M17-Project/M17_3310/M17_3310.kicad_sch

## KiCad design M17_3310.kicad_sch (2025-02-24)

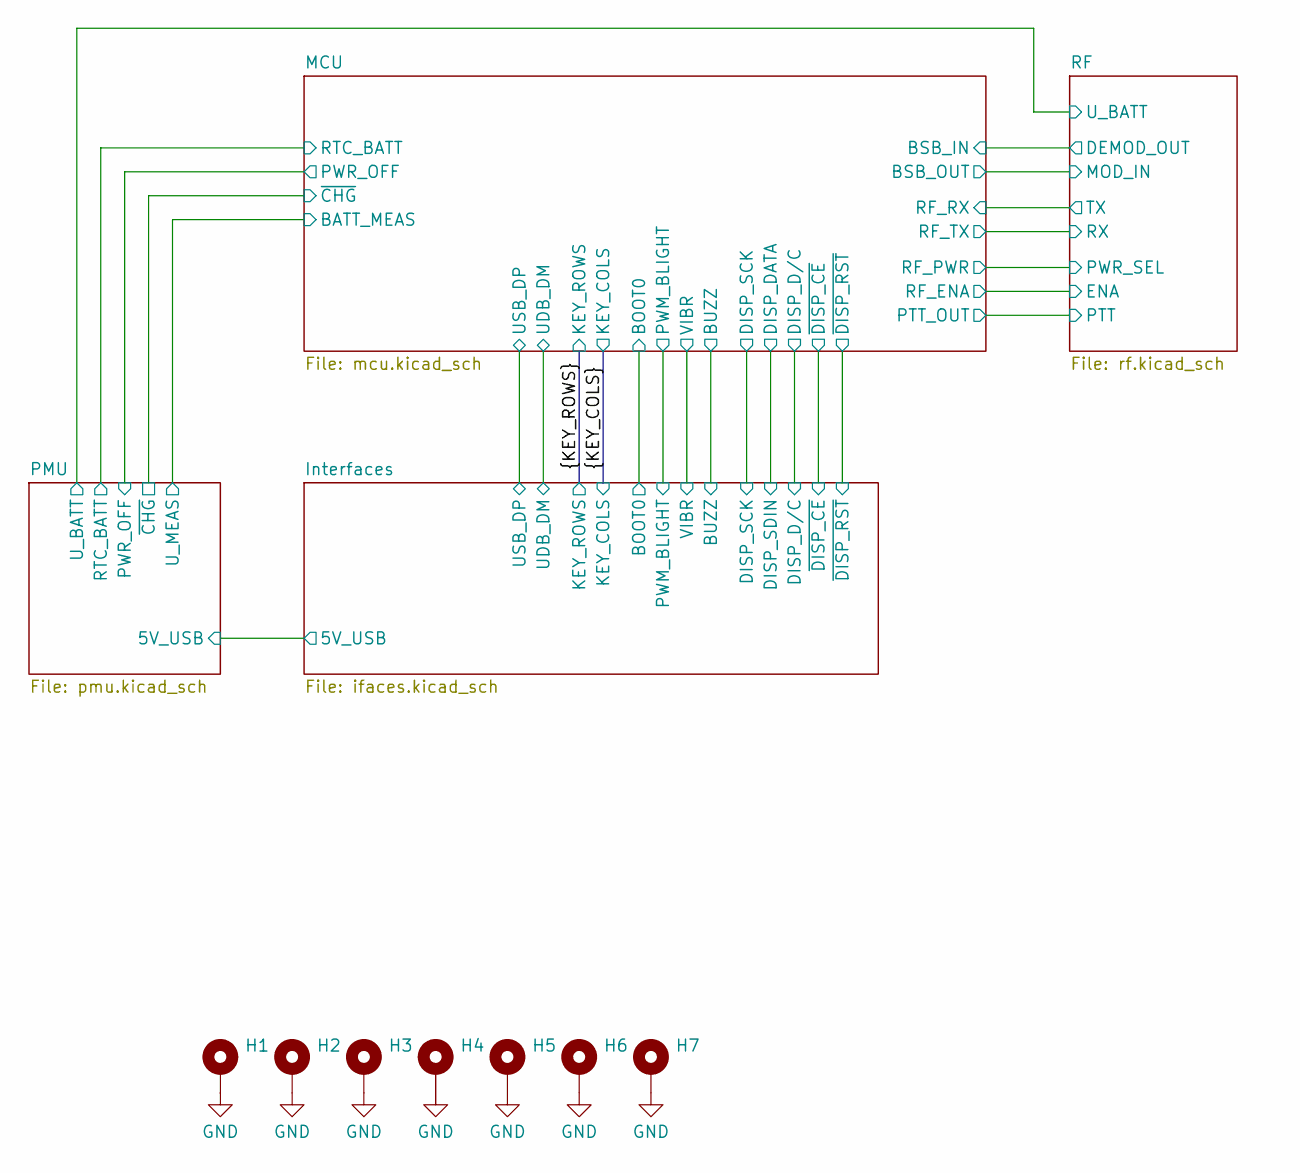
[picture p6: schematic M17_3310.kicad_sch]

Parts:
H1, H2, H3, H4, H5, H6, H7: 2mm_mounting_hole_sig

Connections:
GND: H1.1, H2.1, H3.1, H4.1, H5.1, H6.1, H7.1
