M17-Project/M17_3310/ifaces.kicad_sch

## KiCad design ifaces.kicad_sch (2025-02-24)

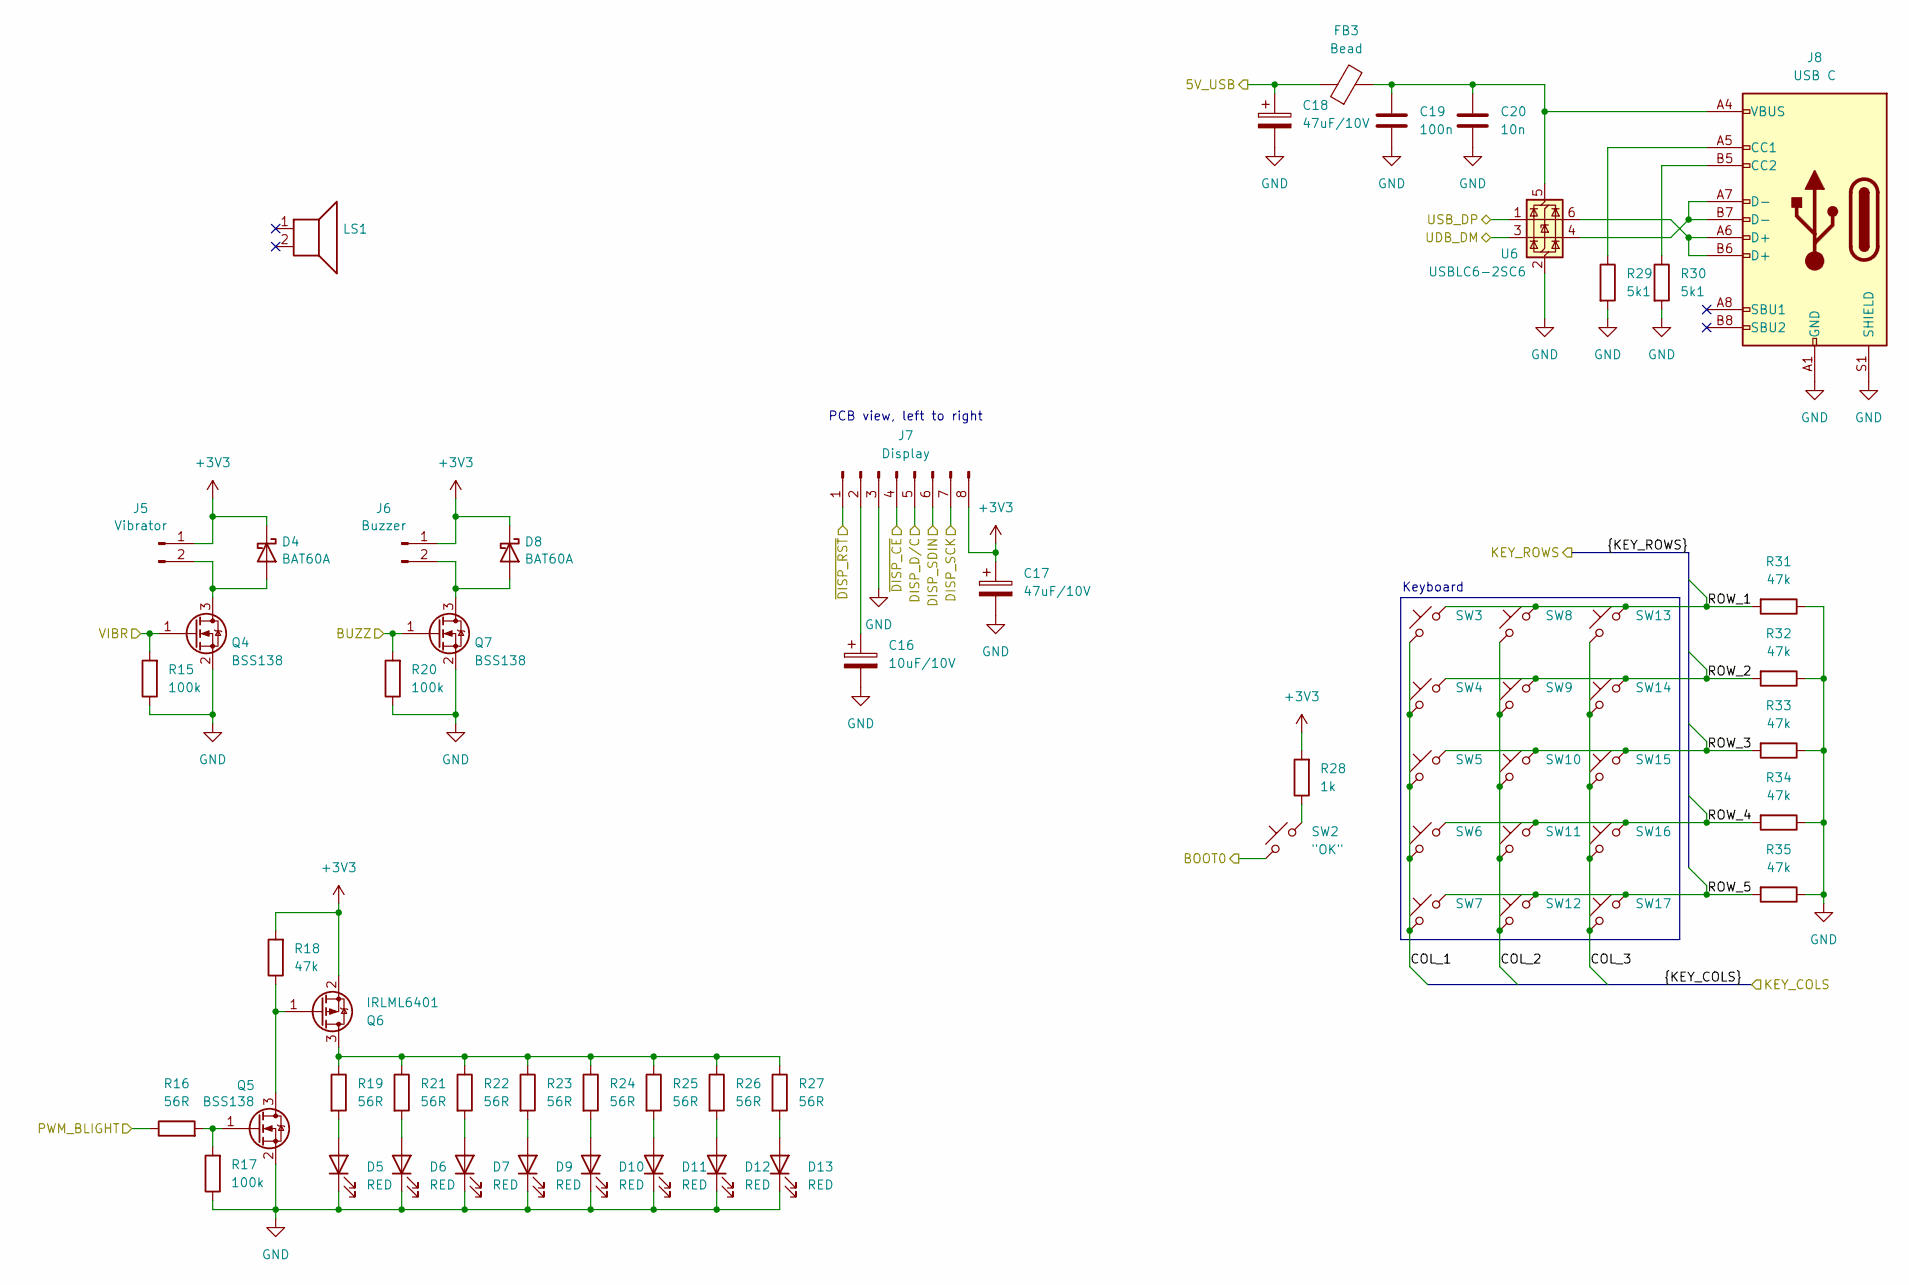
[picture p7: schematic ifaces.kicad_sch]

Parts:
C16: 10uF/10V; CP_EIA-3528-21_Kemet-B; MPN 581-TAJB106K010SNJ
C17, C18: 47uF/10V; CP_EIA-3528-21_Kemet-B; MPN 74-293D476X9010B2TE3
C19: 100n; C_0402_1005Metric; MPN 810-CGA2B3X7R1H104KB
C20: 10n; C_0402_1005Metric; MPN 77-VJ0402Y103KCAAC
D4, D8: BAT60A; D_SOD-323; MPN 726-BAT60AE6327HTSA1
D5, D6, D7, D9, D10, D11, D12, D13: RED; 3310_led; MPN 743-IN-S124ARUR
FB3: Bead; L_0805_2012Metric; MPN 810-MPZ2012S102AT000
J5: Vibrator; 3310_vibrator
J6: Buzzer; 3310_buzzer
J7: Display; 3310_display
J8: USB C; USB_C_Receptacle_GCT_USB4110; MPN 640-USB4110-GF-A
LS1: 3310_speaker
Q4, Q5, Q7: BSS138; SOT-23; MPN 771-BSS138P215
Q6: IRLML6401; SOT-23; MPN 942-IRLML6401TRPBF
R15, R17, R20: 100k; R_0402_1005Metric; MPN 603-RC0402JR-13100KL
R16, R19, R21, R22, R23, R24, R25, R26, R27: 56R; R_0402_1005Metric; MPN 667-ERJ-2GEJ560X
R18, R31, R32, R33, R34, R35: 47k; R_0402_1005Metric; MPN 652-CR0402JW-473GLF
R28: 1k; R_0402_1005Metric; MPN 603-AF0402JR-071KL
R29, R30: 5k1; R_0402_1005Metric; MPN 660-RK73B1ETTP512J
SW2: "OK"; 3310_key
SW3, SW4, SW5, SW6, SW7, SW8, SW9, SW10, SW11, SW12, SW13, SW14, SW15, SW17: 3310_key
SW16: 3310_key_gap
U6: USBLC6-2SC6; SOT-23-6; MPN 511-USBLC6-2SC6

Connections:
5V_USB: C18.1, FB3.1
+3V3: C17.1, D4.1 (K), D8.1 (K), J5.1, J6.1, J7.8, Q6.2 (S), R18.2, R28.2
BOOT0: SW2.1
BUZZ: Q7.1 (G), R20.2
COL_1: SW3.1, SW4.1, SW5.1, SW6.1, SW7.1
COL_2: SW8.1, SW9.1, SW10.1, SW11.1, SW12.1
COL_3: SW13.1, SW14.1, SW15.1, SW16.1, SW17.1
DISP_D/C: J7.5
DISP_SCK: J7.7
DISP_SDIN: J7.6
GND: C16.2, C17.2, C18.2, C19.2, C20.2, D5.1 (K), D6.1 (K), D7.1 (K), D9.1 (K), D10.1 (K), D11.1 (K), D12.1 (K), D13.1 (K), J7.3, J8.A1 (GND), J8.A12 (GND), J8.B1 (GND), J8.B12 (GND), J8.S1 (SHIELD), Q4.2 (S), Q5.2 (S), Q7.2 (S), R15.1, R17.1, R20.1, R29.2, R30.2, R31.1, R32.1, R33.1, R34.1, R35.1, U6.2 (GND)
unnamed: C16.1, J7.2
unnamed: C19.1, C20.1, FB3.2, J8.A4 (VBUS), J8.A9 (VBUS), J8.B4 (VBUS), J8.B9 (VBUS), U6.5 (VBUS)
unnamed: D4.2 (A), J5.2, Q4.3 (D)
unnamed: D5.2 (A), R19.2
unnamed: D6.2 (A), R21.2
unnamed: D7.2 (A), R22.2
unnamed: D8.2 (A), J6.2, Q7.3 (D)
unnamed: D9.2 (A), R23.2
unnamed: D10.2 (A), R24.2
unnamed: D11.2 (A), R25.2
unnamed: D12.2 (A), R26.2
unnamed: D13.2 (A), R27.2
unnamed: J8.A5 (CC1), R29.1
unnamed: J8.A6 (D+), J8.B6 (D+), U6.6 (I/O1)
unnamed: J8.A7 (D-), J8.B7 (D-), U6.4 (I/O2)
unnamed: J8.B5 (CC2), R30.1
unnamed: Q5.1 (G), R16.2, R17.2
unnamed: Q5.3 (D), Q6.1 (G), R18.1
unnamed: Q6.3 (D), R19.1, R21.1, R22.1, R23.1, R24.1, R25.1, R26.1, R27.1
unnamed: R28.1, SW2.2
PWM_BLIGHT: R16.1
ROW_1: R31.2, SW3.2, SW8.2, SW13.2
ROW_2: R32.2, SW4.2, SW9.2, SW14.2
ROW_3: R33.2, SW5.2, SW10.2, SW15.2
ROW_4: R34.2, SW6.2, SW11.2, SW16.2
ROW_5: R35.2, SW7.2, SW12.2, SW17.2
UDB_DM: U6.3 (I/O2)
USB_DP: U6.1 (I/O1)
VIBR: Q4.1 (G), R15.2
~DISP_CE: J7.4
~DISP_RST: J7.1

Notes on the sheet:
Keyboard
PCB view, left to right
