M17-Project/M17_3310/mcu.kicad_sch

## KiCad design mcu.kicad_sch (2025-02-24)

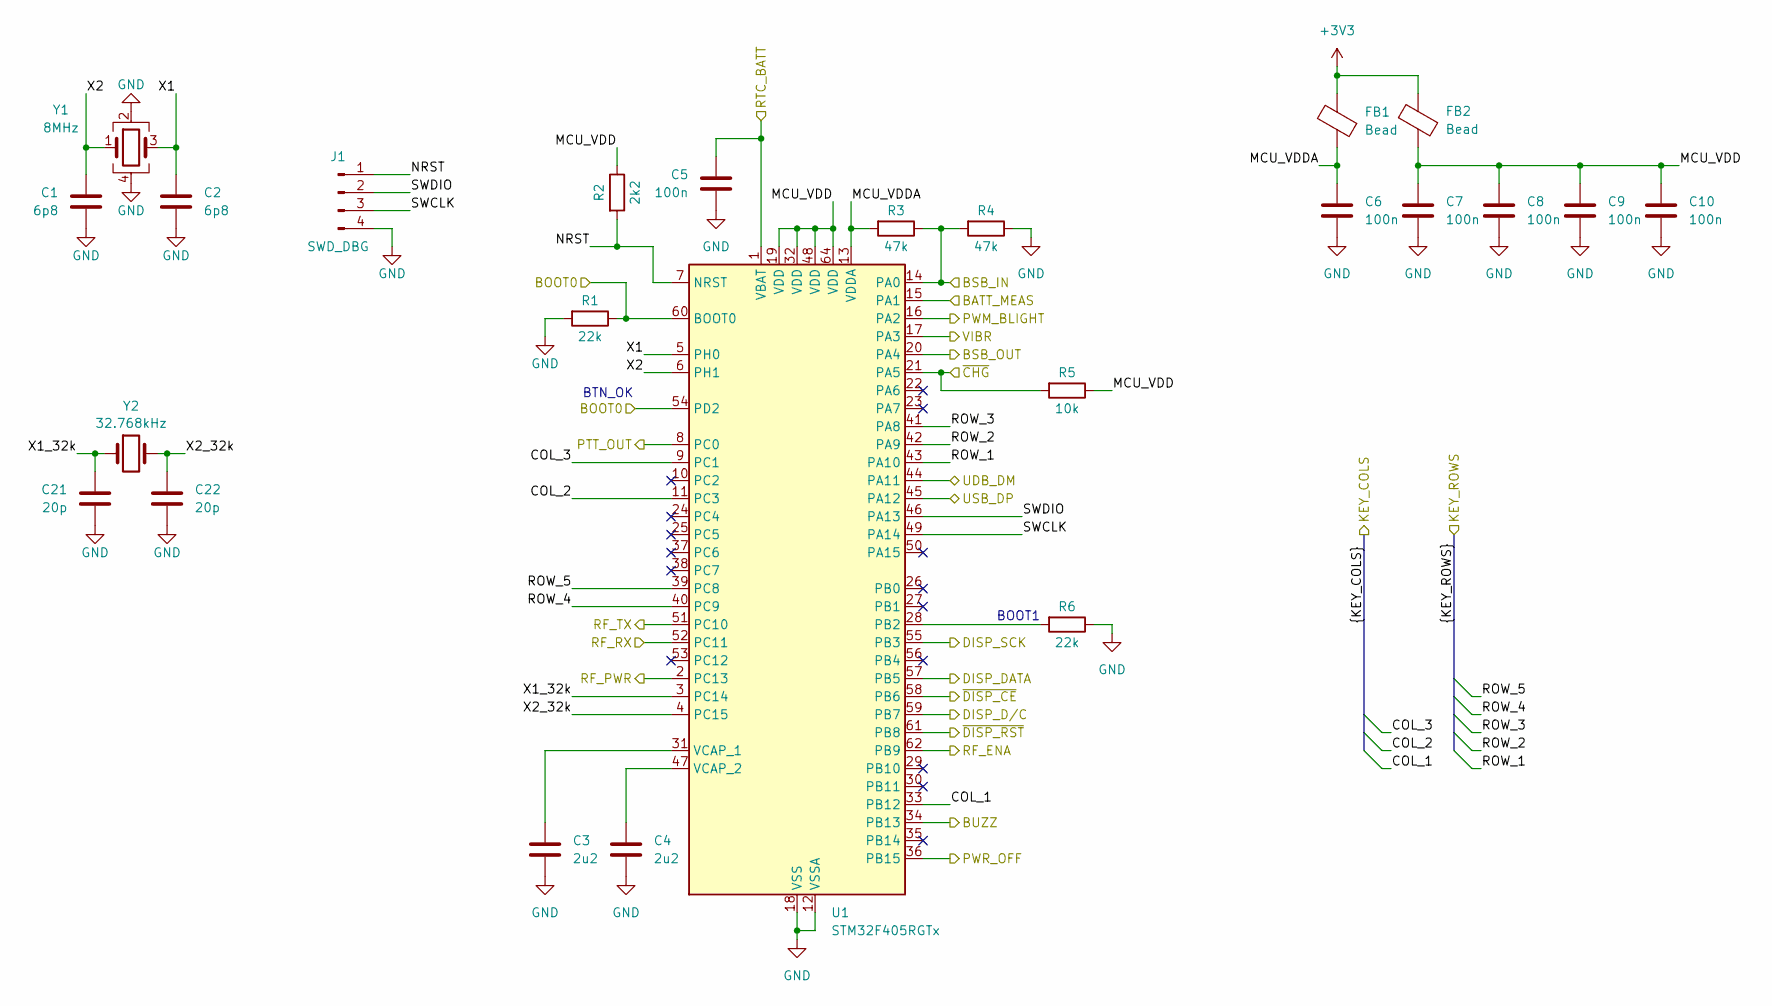
[picture p8: schematic mcu.kicad_sch]

Parts:
C1, C2: 6p8; C_0402_1005Metric; MPN 710-885012005039
C3, C4: 2u2; C_0402_1005Metric; MPN 963-LMK105BJ225MV-F
C5, C6, C7, C8, C9, C10: 100n; C_0402_1005Metric; MPN 810-CGA2B3X7R1H104KB
C21, C22: 20p; C_0402_1005Metric; MPN 81-GCM1555C1H200GA6D
FB1, FB2: Bead; L_0805_2012Metric; MPN 810-MPZ2012S102AT000
J1: SWD_DBG; 3310_4_pin
R1, R6: 22k; R_0402_1005Metric; MPN 279-CRGCQ0402J22K
R2: 2k2; R_0402_1005Metric; MPN 279-CRGCQ0402J2K2
R3, R4: 47k; R_0402_1005Metric; MPN 652-CR0402JW-473GLF
R5: 10k; R_0402_1005Metric; MPN 603-RC0402JR-7D10KL
U1: STM32F405RGTx; LQFP-64_10x10mm_P0.5mm; MPN 511-STM32F405RGT6
Y1: 8MHz; Crystal_SMD_3225-4Pin_3.2x2.5mm; MPN 520-ECS-80-1033CHNTR
Y2: 32.768kHz; xtal_smd_32k

Connections:
+3V3: FB1.2, FB2.1
BATT_MEAS: U1.15 (PA1)
BOOT0: R1.1, U1.54 (PD2), U1.60 (BOOT0)
BSB_IN: R3.1, R4.2, U1.14 (PA0)
BSB_OUT: U1.20 (PA4)
BUZZ: U1.34 (PB13)
COL_1: U1.33 (PB12)
COL_2: U1.11 (PC3)
COL_3: U1.9 (PC1)
DISP_DATA: U1.57 (PB5)
DISP_D/C: U1.59 (PB7)
DISP_SCK: U1.55 (PB3)
GND: C1.2, C2.2, C3.1, C4.1, C5.1, C6.1, C7.2, C8.2, C9.2, C10.2, C21.2, C22.1, J1.4, R1.2, R4.1, R6.1, U1.12 (VSSA), U1.18 (VSS), U1.63 (VSS), Y1.2, Y1.4
MCU_VDD: C7.1, C8.1, C9.1, C10.1, FB2.2, R2.1, R5.1, U1.19 (VDD), U1.32 (VDD), U1.48 (VDD), U1.64 (VDD)
MCU_VDDA: C6.2, FB1.1, R3.2, U1.13 (VDDA)
NRST: J1.1, R2.2, U1.7 (NRST)
unnamed: C3.2, U1.31 (VCAP_1)
unnamed: C4.2, U1.47 (VCAP_2)
unnamed: R6.2, U1.28 (PB2)
PTT_OUT: U1.8 (PC0)
PWM_BLIGHT: U1.16 (PA2)
PWR_OFF: U1.36 (PB15)
RF_ENA: U1.62 (PB9)
RF_PWR: U1.2 (PC13)
RF_RX: U1.52 (PC11)
RF_TX: U1.51 (PC10)
ROW_1: U1.43 (PA10)
ROW_2: U1.42 (PA9)
ROW_3: U1.41 (PA8)
ROW_4: U1.40 (PC9)
ROW_5: U1.39 (PC8)
RTC_BATT: C5.2, U1.1 (VBAT)
SWCLK: J1.3, U1.49 (PA14)
SWDIO: J1.2, U1.46 (PA13)
UDB_DM: U1.44 (PA11)
USB_DP: U1.45 (PA12)
VIBR: U1.17 (PA3)
X1: C2.1, U1.5 (PH0), Y1.3
X1_32k: C21.1, U1.3 (PC14), Y2.1
X2: C1.1, U1.6 (PH1), Y1.1
X2_32k: C22.2, U1.4 (PC15), Y2.2
~CHG: R5.2, U1.21 (PA5)
~DISP_CE: U1.58 (PB6)
~DISP_RST: U1.61 (PB8)

Notes on the sheet:
BOOT1
BTN_OK
