M17-Project/M17_3310/pmu.kicad_sch

## KiCad design pmu.kicad_sch (2025-02-24)

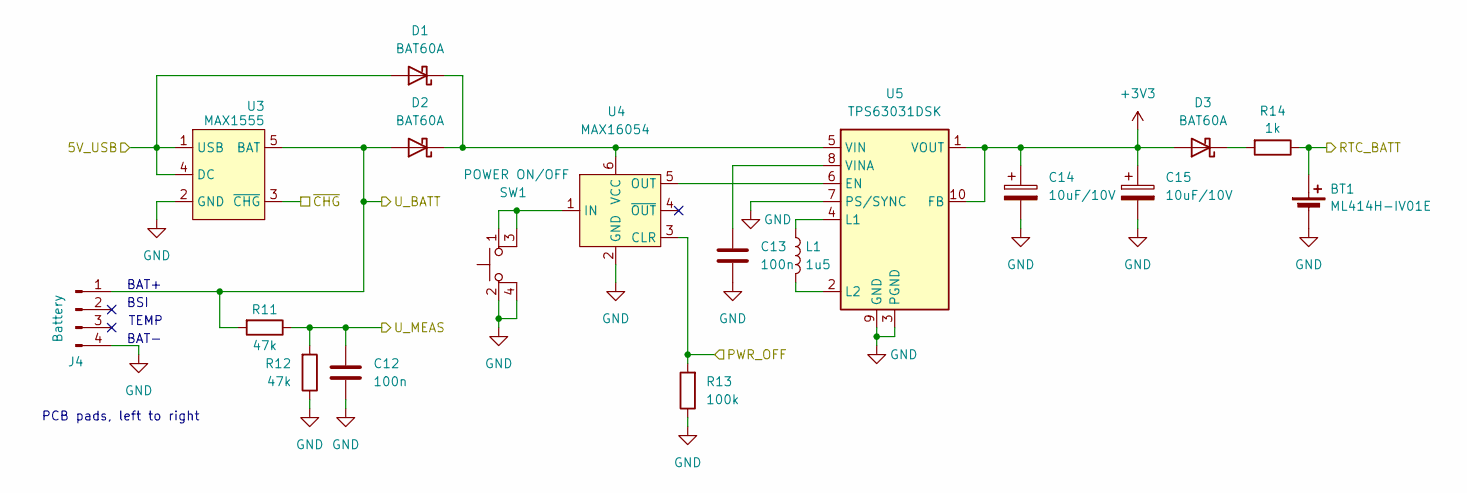
[picture p9: schematic pmu.kicad_sch]

Parts:
BT1: ML414H-IV01E; ML414H; MPN ML414H-IV01E
C12, C13: 100n; C_0402_1005Metric; MPN 810-CGA2B3X7R1H104KB
C14, C15: 10uF/10V; CP_EIA-3528-21_Kemet-B; MPN 581-TAJB106K010SNJ
D1, D2, D3: BAT60A; D_SOD-323; MPN 726-BAT60AE6327HTSA1
J4: Battery; 3310_batt
L1: 1u5; L_1210_3225Metric; MPN 963-LBC3225T1R5MR
R11, R12: 47k; R_0402_1005Metric; MPN 652-CR0402JW-473GLF
R13: 100k; R_0402_1005Metric; MPN 603-RC0402JR-13100KL
R14: 1k; R_0402_1005Metric; MPN 603-AF0402JR-071KL
SW1: POWER ON/OFF; SIDE PUSH 2.2NF 4.7x3.2x1.65mm; MPN 667-EVQ-PUA02K
U3: MAX1555; TSOT-23-5; MPN 700-MAX1555EZK+T
U4: MAX16054; TSOT-23-6; MPN 700-MAX16054AZTT
U5: TPS63031DSK; WSON-10-1EP_2.5x2.5mm_P0.5mm_EP1.2x2mm; MPN 595-TPS63031DSKR

Connections:
5V_USB: D1.2 (A), U3.1 (USB), U3.4 (DC)
+3V3: C14.1, C15.1, D3.2 (A), U5.1 (VOUT), U5.10 (FB)
GND: BT1.2 (-), C12.1, C13.1, C14.2, C15.2, J4.4, R12.1, R13.1, SW1.2, SW1.4 (A), U3.2 (GND), U4.2 (GND), U5.3 (PGND), U5.7 (PS/SYNC), U5.9 (GND), U5.11 (PGND)
unnamed: C13.2, U5.8 (VINA)
unnamed: D1.1 (K), D2.1 (K), U4.6 (VCC), U5.5 (VIN)
unnamed: D3.1 (K), R14.2
unnamed: L1.1, U5.4 (L1)
unnamed: L1.2, U5.2 (L2)
unnamed: SW1.1, SW1.3 (K), U4.1 (IN)
unnamed: U4.5 (OUT), U5.6 (EN)
PWR_OFF: R13.2, U4.3 (CLR)
RTC_BATT: BT1.1 (+), R14.1
U_BATT: D2.2 (A), J4.1, R11.2, U3.5 (BAT)
U_MEAS: C12.2, R11.1, R12.2
~CHG: U3.3 (~CHG)

Notes on the sheet:
BAT+
BAT-
TEMP
PCB pads, left to right
BSI
