M17-Project/M17_3310/rf.kicad_sch

## KiCad design rf.kicad_sch (2025-02-24)

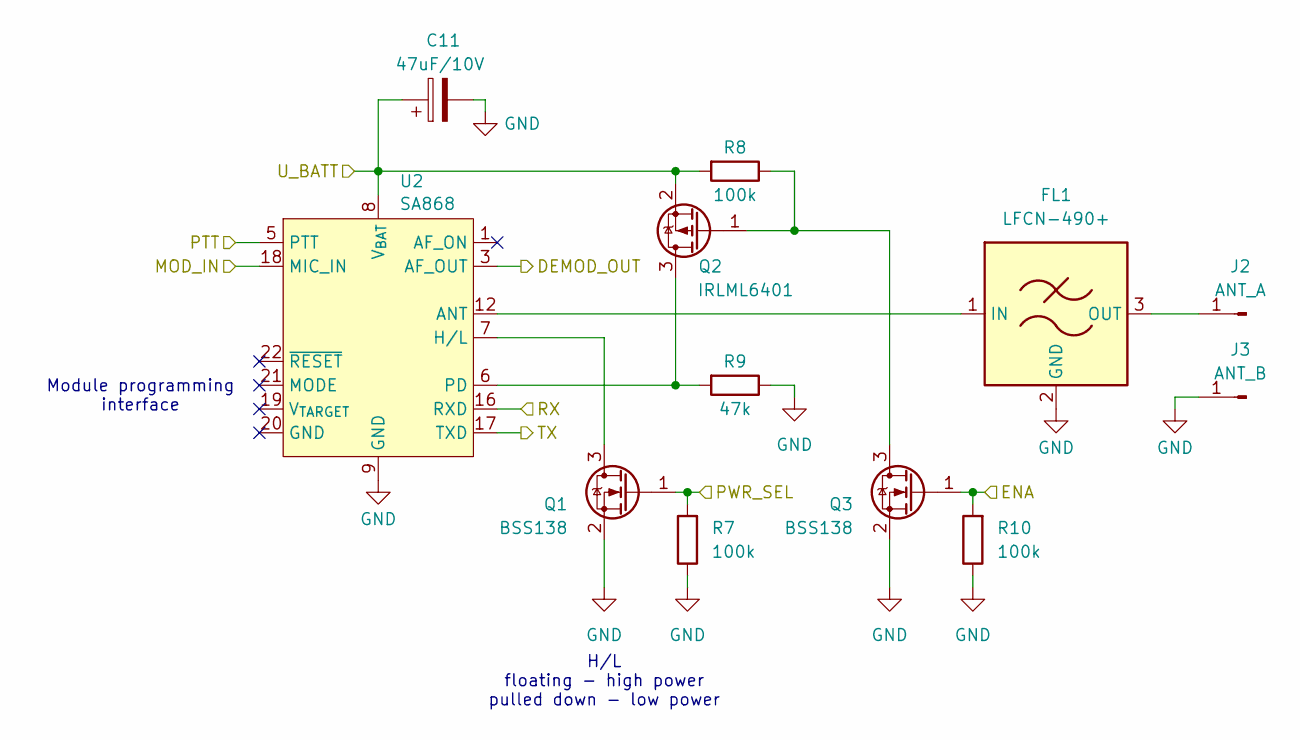
[picture p10: schematic rf.kicad_sch]

Parts:
C11: 47uF/10V; CP_EIA-3528-21_Kemet-B; MPN 74-293D476X9010B2TE3
FL1: LFCN-490+; Filter_Mini-Circuits_FV1206; MPN 139-LFCN-490
J2: ANT_A; TestPoint_Pad_D1.5mm
J3: ANT_B; TestPoint_Pad_D1.5mm
Q1, Q3: BSS138; SOT-23; MPN 771-BSS138P215
Q2: IRLML6401; SOT-23; MPN 942-IRLML6401TRPBF
R7, R8, R10: 100k; R_0402_1005Metric; MPN 603-RC0402JR-13100KL
R9: 47k; R_0402_1005Metric; MPN 652-CR0402JW-473GLF
U2: SA868; SA868-VER1.1; MPN SA868S-U

Connections:
DEMOD_OUT: U2.3 (AF_OUT)
ENA: Q3.1 (G), R10.2
GND: C11.2, FL1.2 (GND), FL1.4 (GND), J3.1, Q1.2 (S), Q3.2 (S), R7.1, R9.1, R10.1, U2.9 (GND), U2.10 (GND)
MOD_IN: U2.18 (MIC_IN)
unnamed: FL1.1 (IN), U2.12 (ANT)
unnamed: FL1.3 (OUT), J2.1
unnamed: Q1.3 (D), U2.7 (H/L)
unnamed: Q2.1 (G), Q3.3 (D), R8.1
unnamed: Q2.3 (D), R9.2, U2.6 (PD)
PTT: U2.5 (PTT)
PWR_SEL: Q1.1 (G), R7.2
RX: U2.16 (RXD)
TX: U2.17 (TXD)
U_BATT: C11.1, Q2.2 (S), R8.2, U2.8 (V_{BAT})

Notes on the sheet:
H/L floating - high power pulled down - low power
Module programming interface
